andrewerrington/battmanpi/battmanpi/tkSimpleDialog.py

# tkDialog helper from
# http://effbot.org/tkinterbook/tkinter-dialog-windows.htm
# This software may differ from the original

# Copyright © 1995-2014 by Fredrik Lundh

# By obtaining, using, and/or copying this software and/or its associated
# documentation, you agree that you have read, understood, and will comply
# with the following terms and conditions:

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

import tkinter as tk
from tkinter import ttk

import os

class Dialog(tk.Toplevel):

    def __init__(self, parent, title = None, **kwargs):

        tk.Toplevel.__init__(self, parent)
        self.transient(parent)

        if title:
            self.title(title)

        self.parent = parent

        self.result = None

        self.kwargs = kwargs

        body = ttk.Frame(self)
        self.initial_focus = self.body(body)
        #body.pack(padx=5, pady=5)      # FIXME: we're using grid

        self.buttonbox()

        self.grab_set()

        if not self.initial_focus:
            self.initial_focus = self

        self.protocol("WM_DELETE_WINDOW", self.cancel)

        #self.geometry("+%d+%d" % (parent.winfo_rootx()+50,     # FIXME: doesn't work
        #                          parent.winfo_rooty()+50))

        self.initial_focus.focus_set()

        self.wait_window(self)

    #
    # construction hooks

    def body(self, master):
        # create dialog body.  return widget that should have
        # initial focus.  this method should be overridden

        pass

    def buttonbox(self):
        # add standard button box. override if you don't want the
        # standard buttons

        box = Frame(self)

        w = Button(box, text="OK", width=10, command=self.ok, default=ACTIVE)
        w.pack(side=LEFT, padx=5, pady=5)
        w = Button(box, text="Cancel", width=10, command=self.cancel)
        w.pack(side=LEFT, padx=5, pady=5)

        self.bind("<Return>", self.ok)
        self.bind("<Escape>", self.cancel)

        box.pack()

    #
    # standard button semantics

    def ok(self, event=None):

        if not self.validate():
            self.initial_focus.focus_set() # put focus back
            return

        self.withdraw()
        self.update_idletasks()

        self.apply()

        self.cancel()

    def cancel(self, event=None):

        # put focus back to the parent window
        #self.parent.focus_set() FIXME: doesn't work
        self.destroy()

    #
    # command hooks

    def validate(self):

        return 1 # override

    def apply(self):

        pass # override
